atechofficials/protokeeb/Images/KB_Images/Protokeeb_1.png

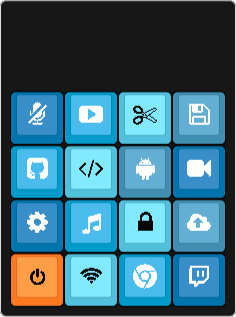
Images/KB_Images/Protokeeb_1.png
