atechofficials/protokeeb/Images/KB_Images/Protokeeb_3.jpg

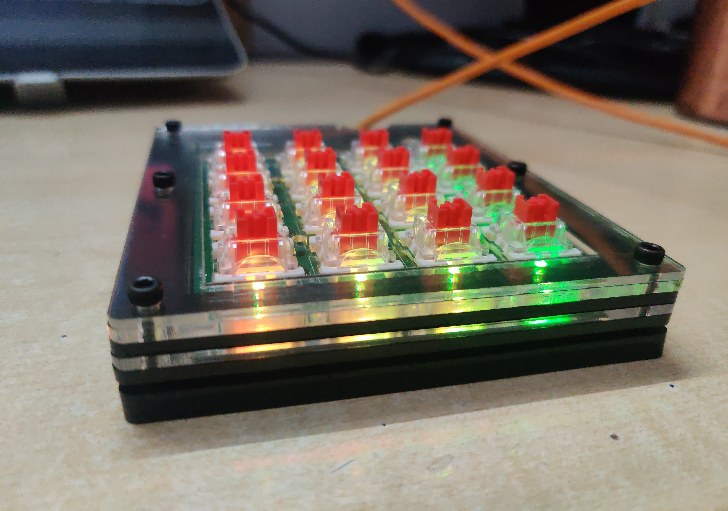
Images/KB_Images/Protokeeb_3.jpg
