atechofficials/protokeeb/Images/KB_Images/Protokeeb_3D-1.jpg

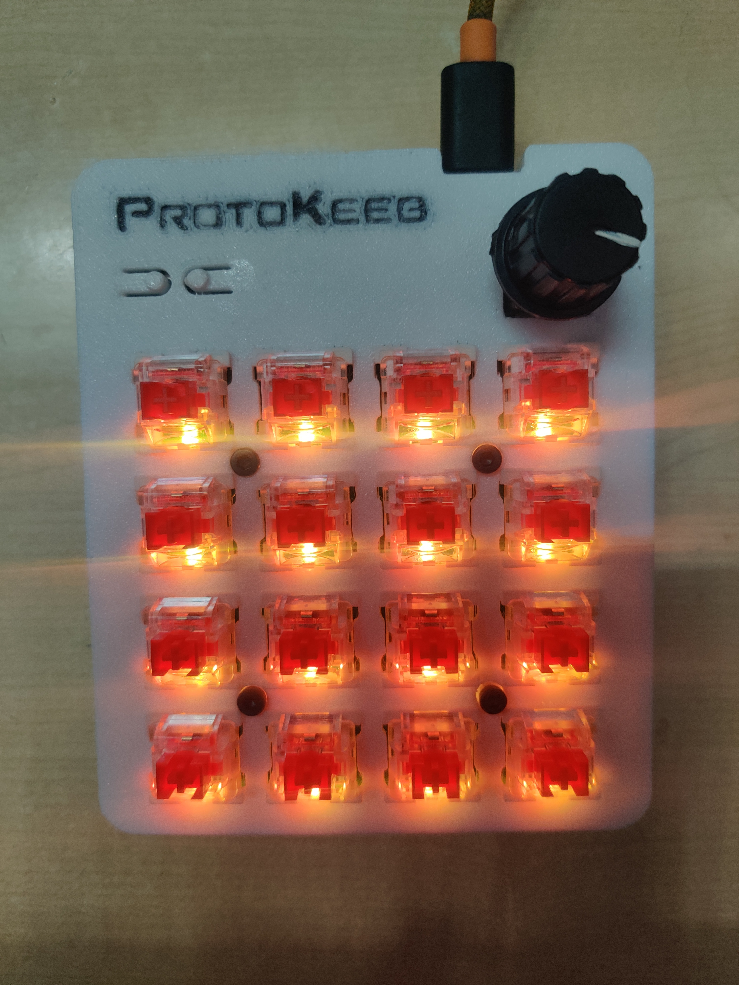
Images/KB_Images/Protokeeb_3D-1.jpg
