atechofficials/protokeeb/Images/KB_Images/Protokeeb_3D-2.jpg

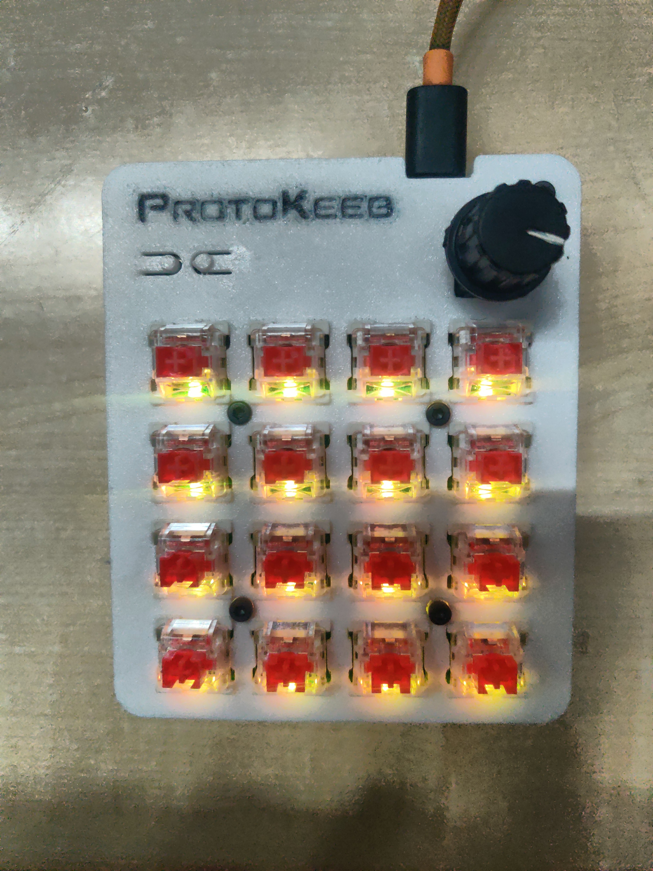
Images/KB_Images/Protokeeb_3D-2.jpg
