atechofficials/protokeeb/Images/KB_Images/Protokeeb_3D-3.jpg

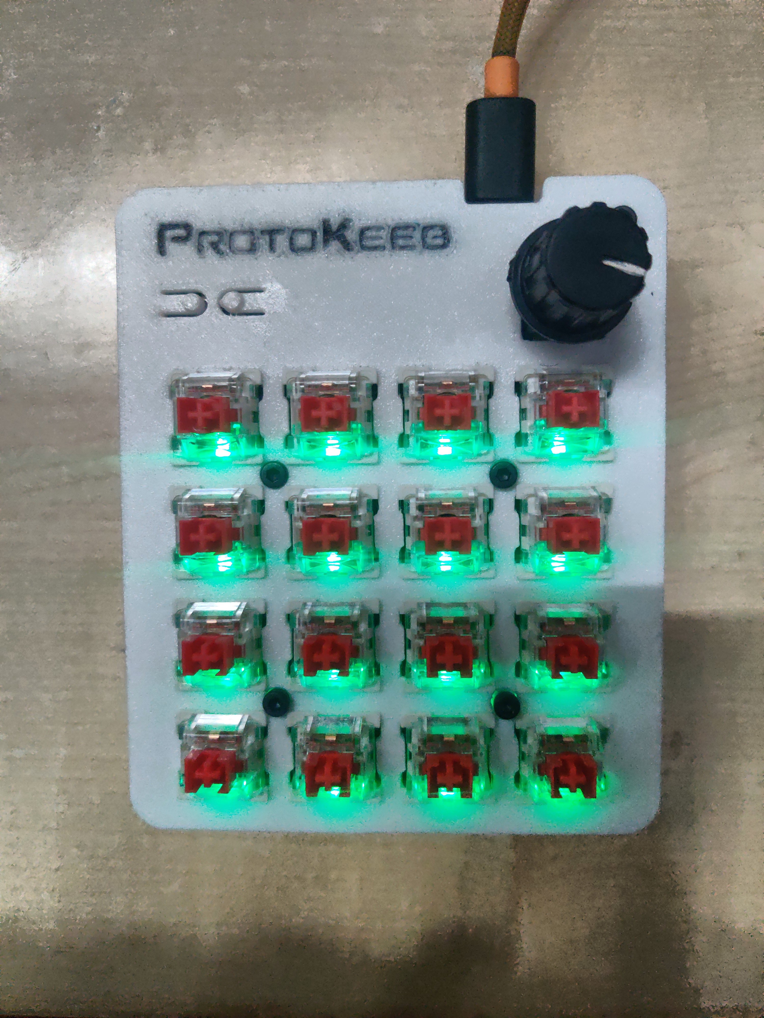
Images/KB_Images/Protokeeb_3D-3.jpg
