atechofficials/protokeeb/Images/KB_Images/Protokeeb_3D-4.jpg

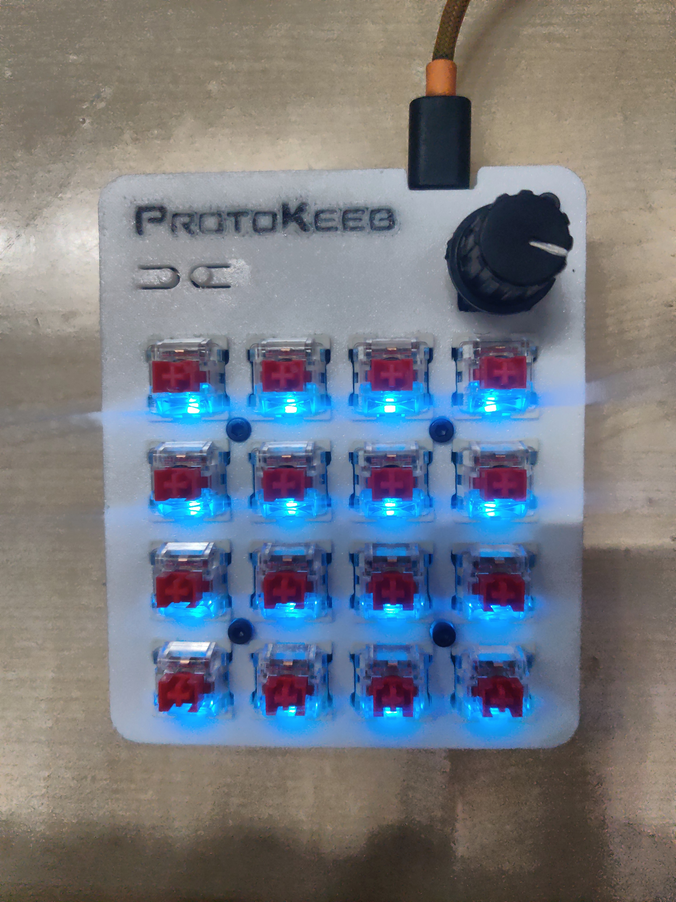
Images/KB_Images/Protokeeb_3D-4.jpg
