atechofficials/protokeeb/Images/KB_Images/Protokeeb_3D-5.jpg

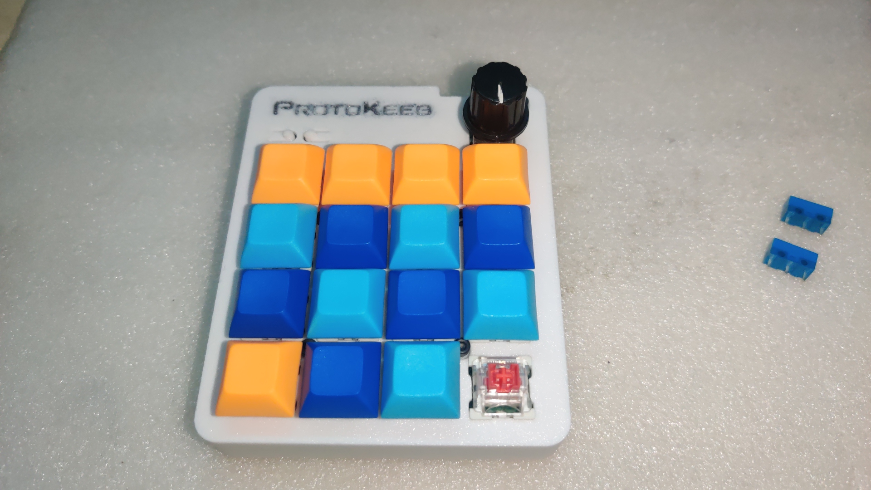
Images/KB_Images/Protokeeb_3D-5.jpg
