atechofficials/protokeeb/Images/KB_Images/Protokeeb_3D-6.jpg

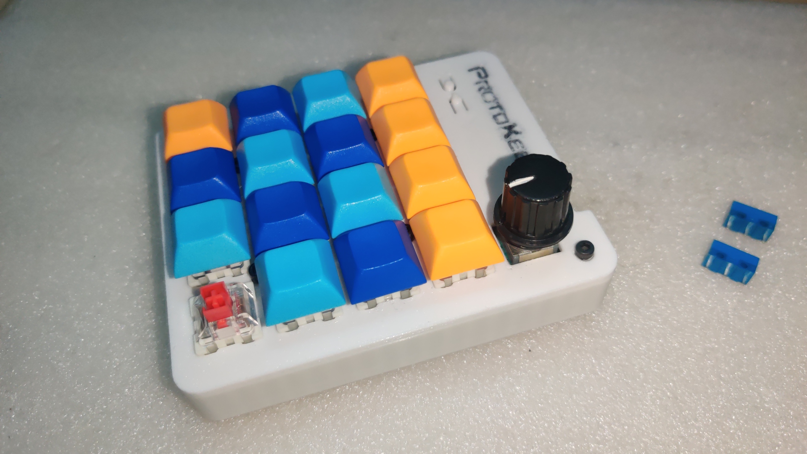
Images/KB_Images/Protokeeb_3D-6.jpg
