atechofficials/protokeeb/Images/KB_Images/Protokeeb_3D-7.jpg

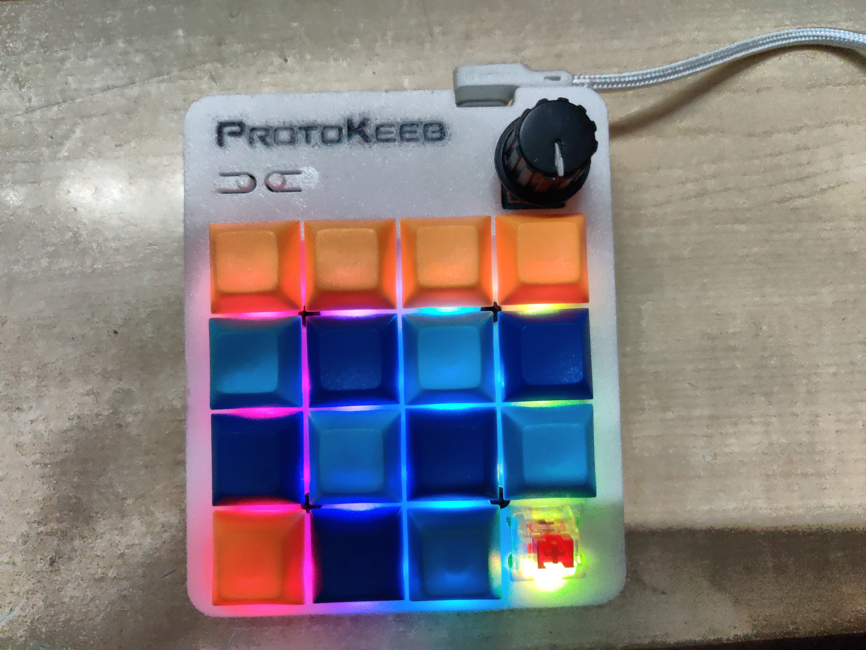
Images/KB_Images/Protokeeb_3D-7.jpg
