atechofficials/protokeeb/Images/KB_Images/Protokeeb_3D-8.jpg

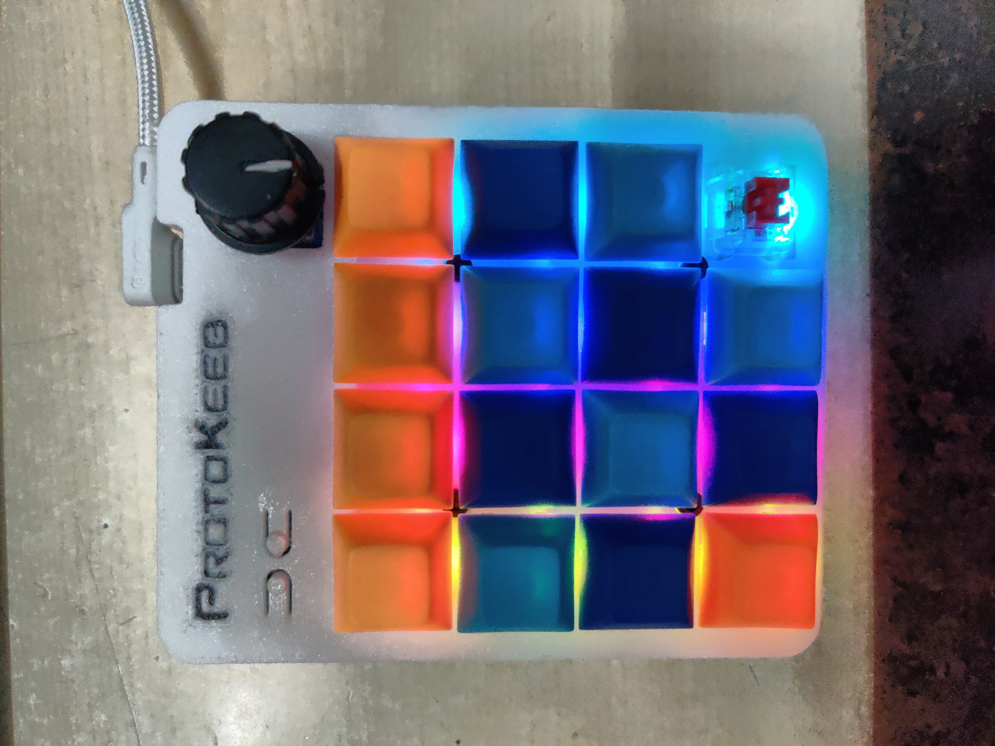
Images/KB_Images/Protokeeb_3D-8.jpg
