atechofficials/protokeeb/Images/KB_Images/Protokeeb_3D-9.jpg

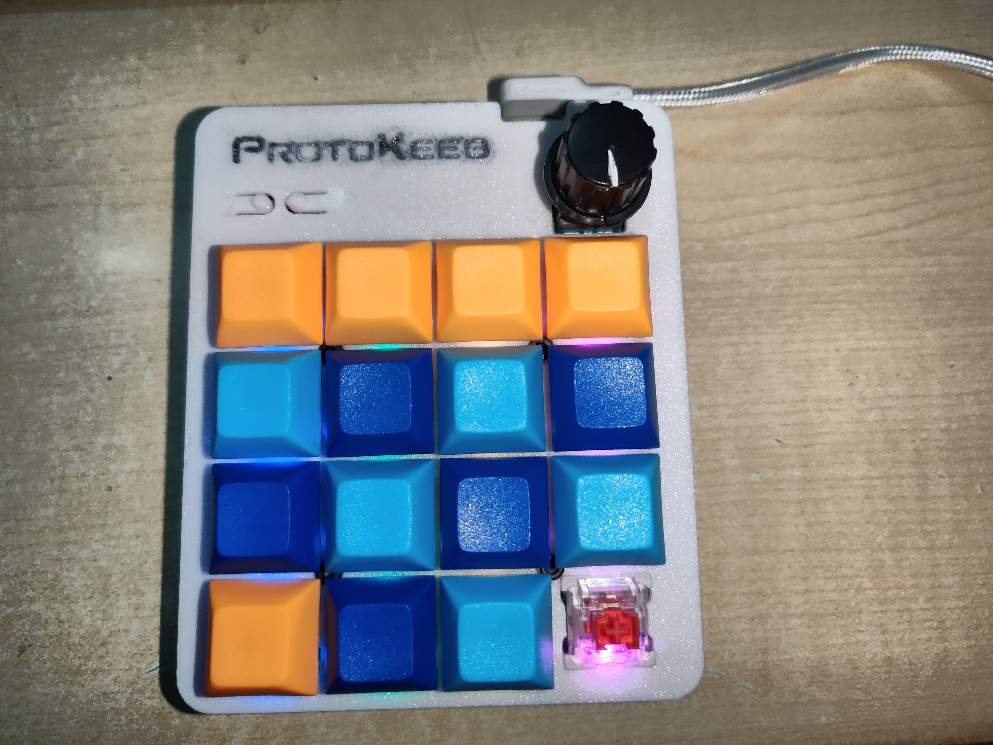
Images/KB_Images/Protokeeb_3D-9.jpg
