atechofficials/protokeeb/Images/KB_Images/Protokeeb_3D-10.jpg

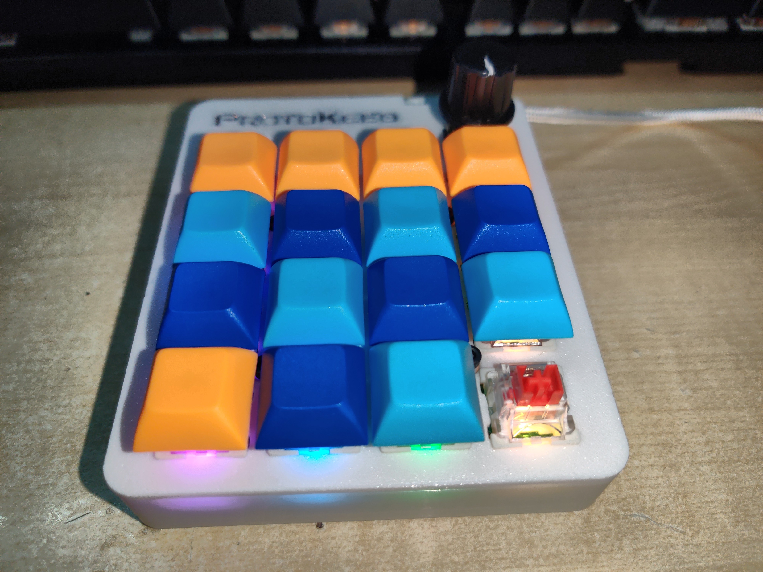
Images/KB_Images/Protokeeb_3D-10.jpg
