atechofficials/protokeeb/Images/KB_Images/Protokeeb_3D-11.jpg

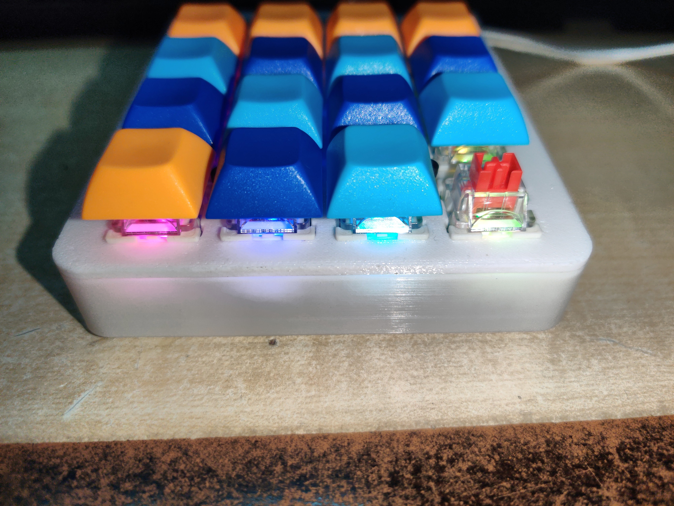
Images/KB_Images/Protokeeb_3D-11.jpg
