atechofficials/protokeeb/Images/KB_Images/Protokeeb_3D-14.jpg

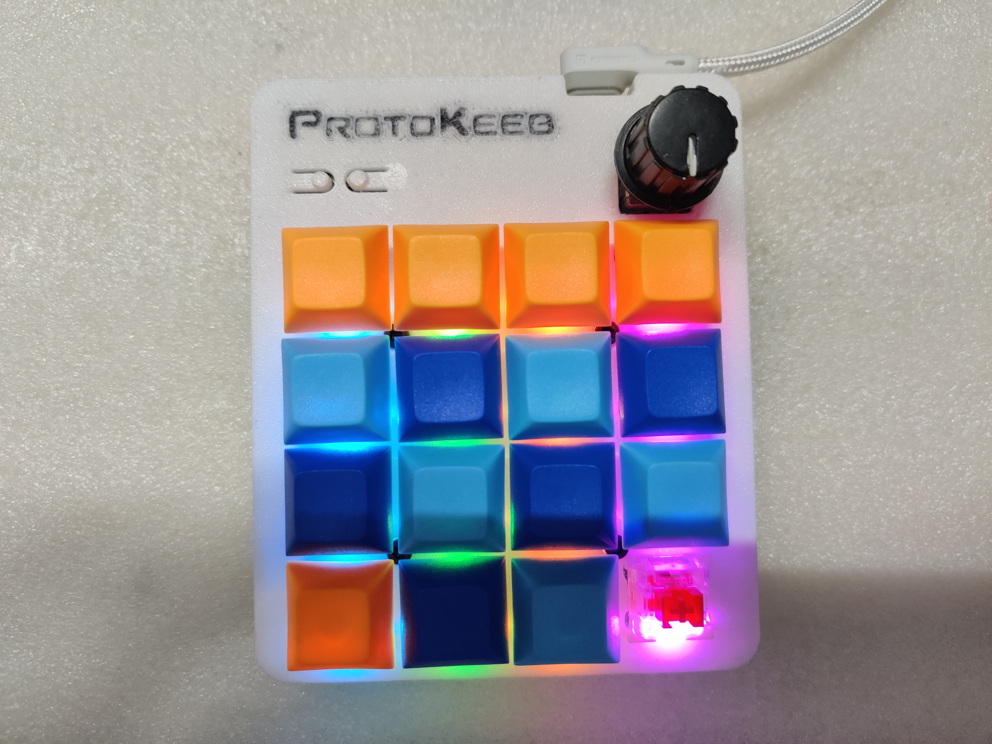
Images/KB_Images/Protokeeb_3D-14.jpg
