atechofficials/protokeeb/Images/KB_Images/Protokeeb_3D-15.jpg

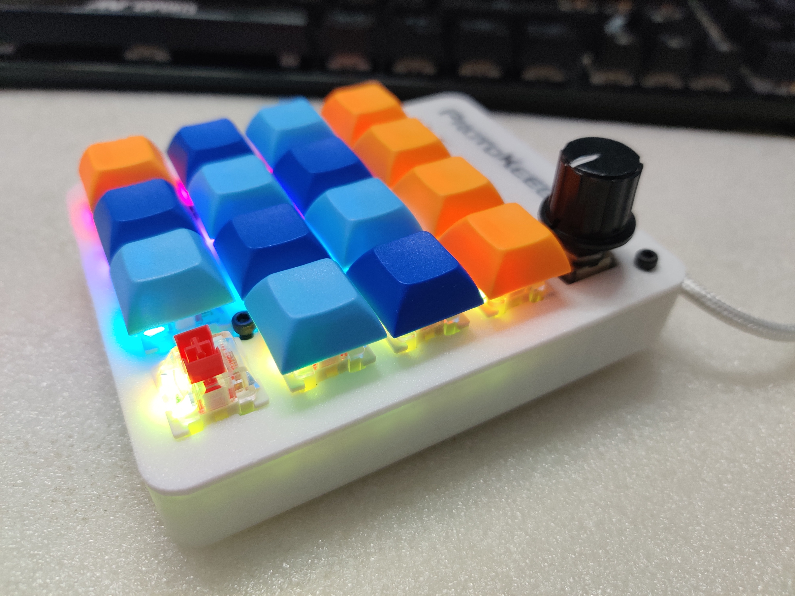
Images/KB_Images/Protokeeb_3D-15.jpg
