atechofficials/protokeeb/Images/KB_Images/Protokeeb_3D-16.jpg

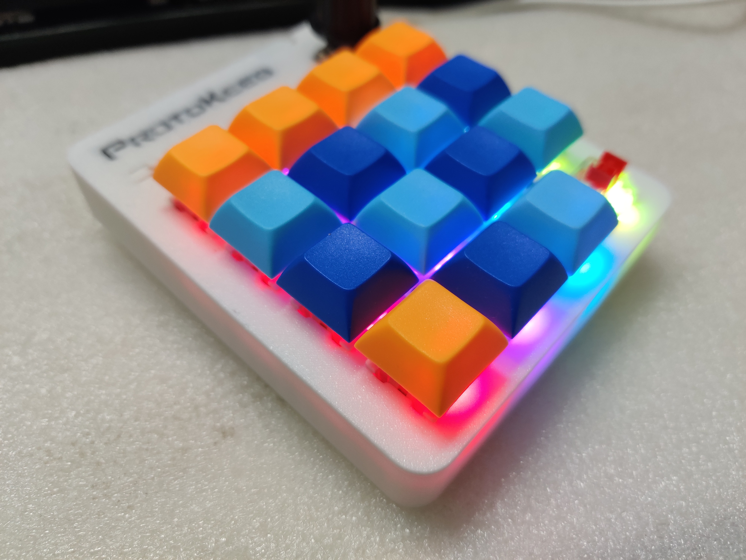
Images/KB_Images/Protokeeb_3D-16.jpg
