atechofficials/protokeeb/Images/KB_Images/Protokeeb_3D-17.jpg

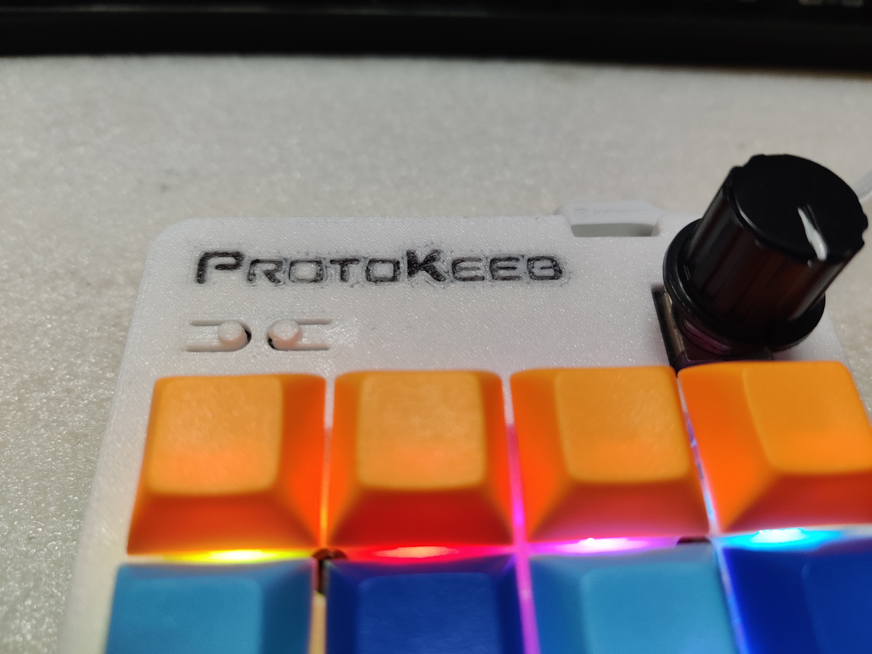
Images/KB_Images/Protokeeb_3D-17.jpg
