atechofficials/protokeeb/Images/KB_Images/Protokeeb_3D-18.jpg

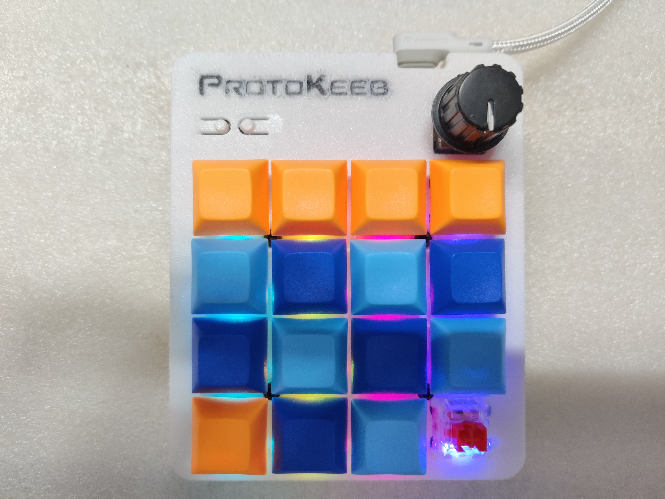
Images/KB_Images/Protokeeb_3D-18.jpg
