atechofficials/protokeeb/Images/KB_Images/Protokeeb_3D-19.jpg

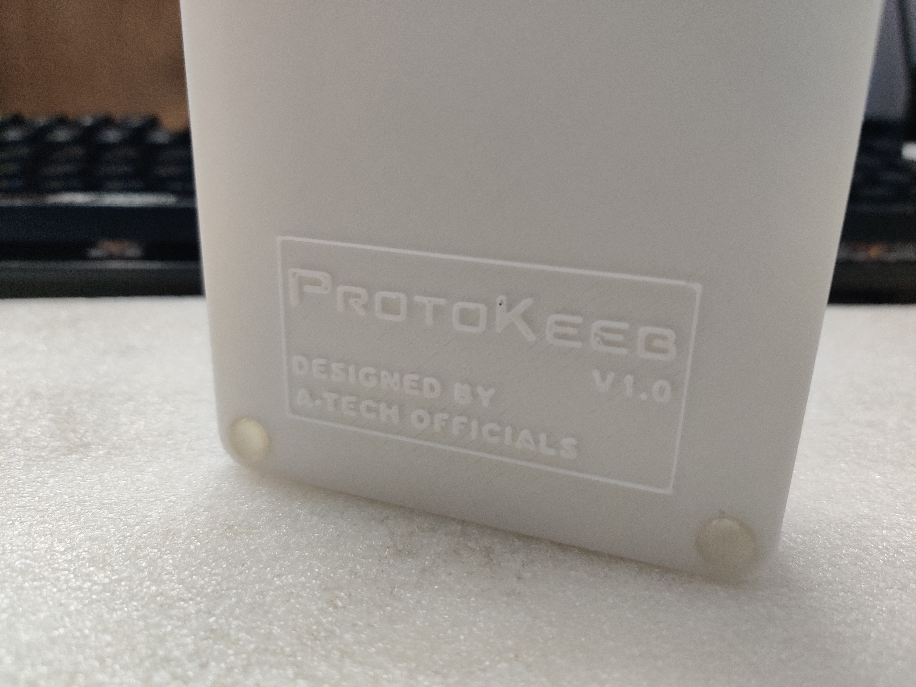
Images/KB_Images/Protokeeb_3D-19.jpg
