atechofficials/protokeeb/Images/KB_Images/Protokeeb_4.jpg

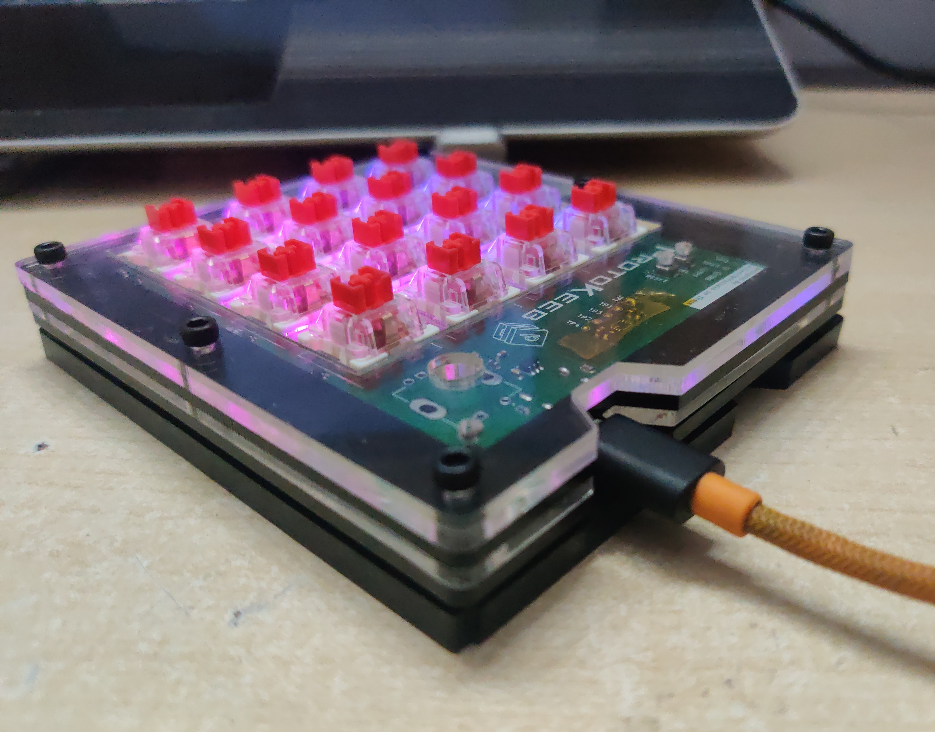
Images/KB_Images/Protokeeb_4.jpg
