atechofficials/protokeeb/Images/KB_Images/protokeeb_via_layout.png

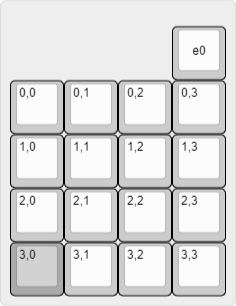
Images/KB_Images/protokeeb_via_layout.png
