atechofficials/protokeeb/Images/PCB_Images/Protokeeb_PCB_1.jpg

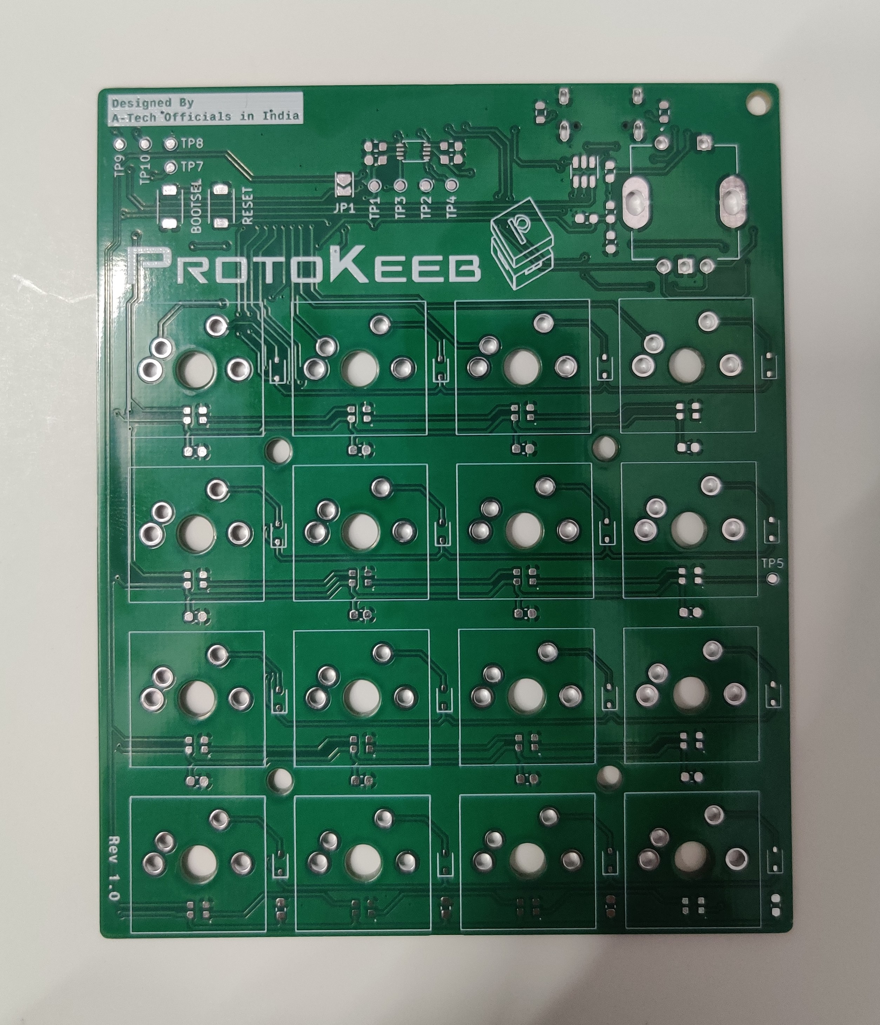
Images/PCB_Images/Protokeeb_PCB_1.jpg
