atechofficials/protokeeb/Images/PCB_Images/Protokeeb_PCB_2.jpg

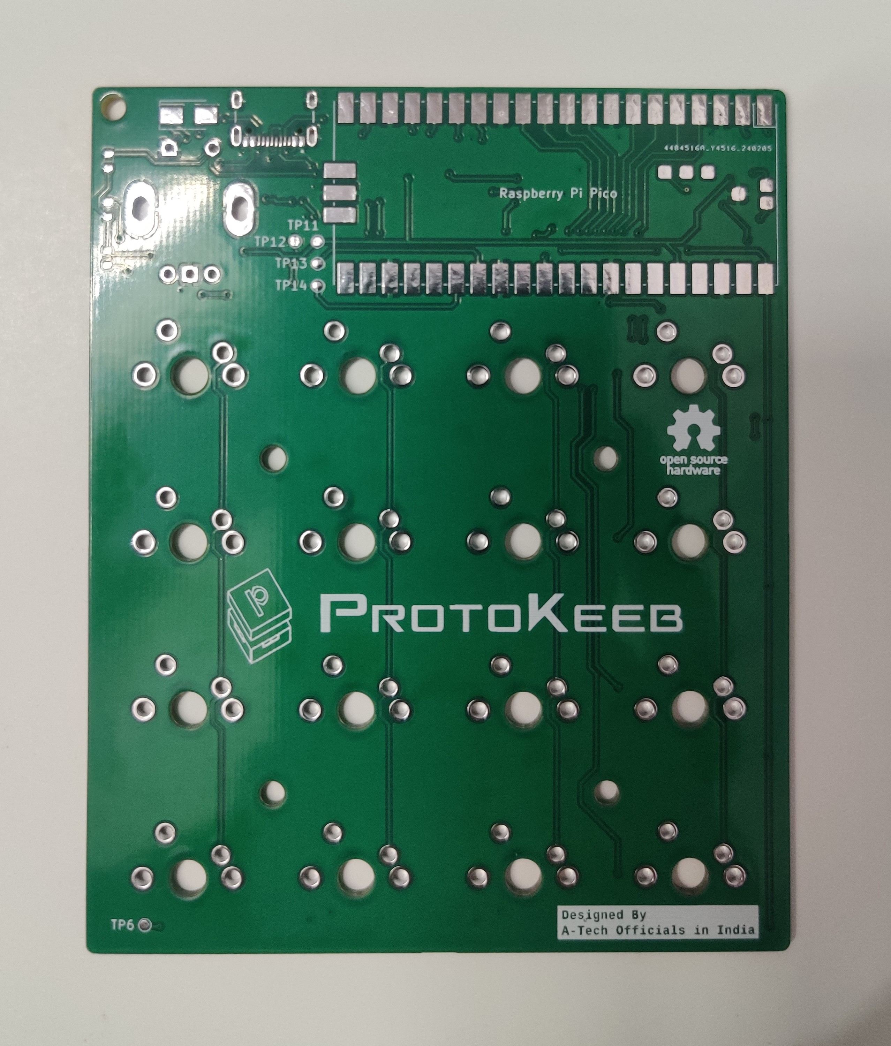
Images/PCB_Images/Protokeeb_PCB_2.jpg
