atechofficials/protokeeb/Images/PCB_Images/Protokeeb_PCB_3.jpg

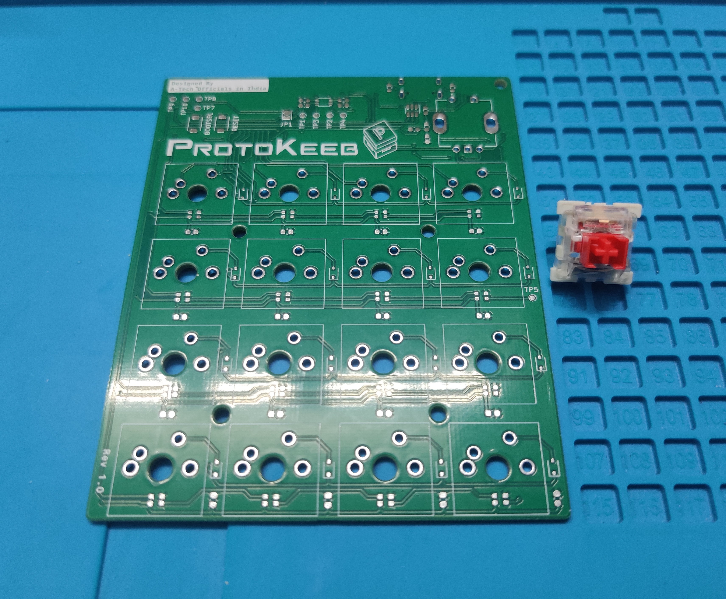
Images/PCB_Images/Protokeeb_PCB_3.jpg
