atechofficials/protokeeb/Images/PCB_Renders/AT-ProtoKeeb_rev1_1.png

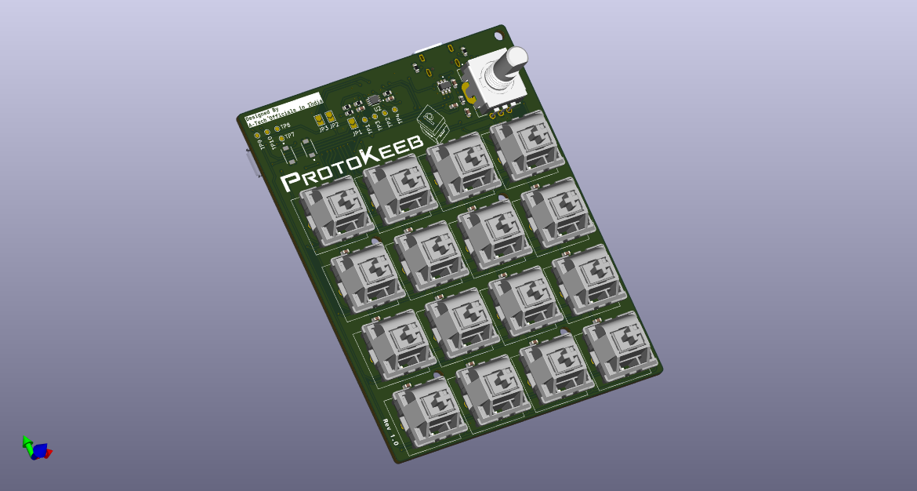
Images/PCB_Renders/AT-ProtoKeeb_rev1_1.png
