atechofficials/protokeeb/Images/PCB_Renders/AT-ProtoKeeb_rev1_2.png

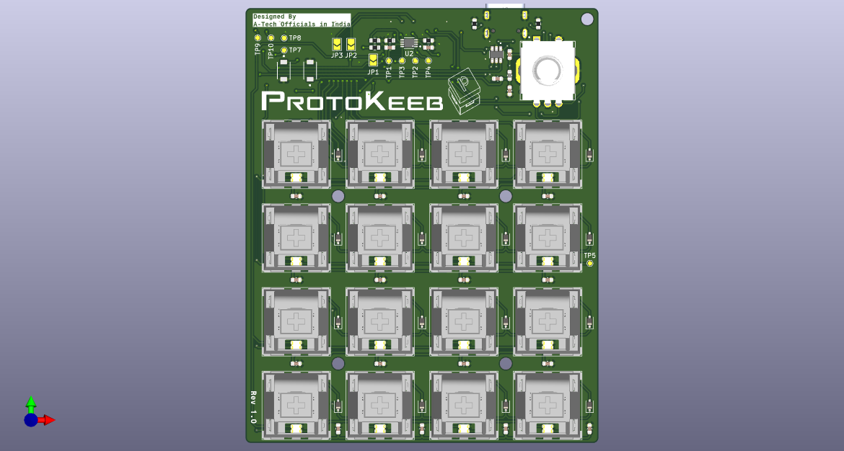
Images/PCB_Renders/AT-ProtoKeeb_rev1_2.png
