atechofficials/protokeeb/Images/PCB_Renders/AT-ProtoKeeb_rev1_3.png

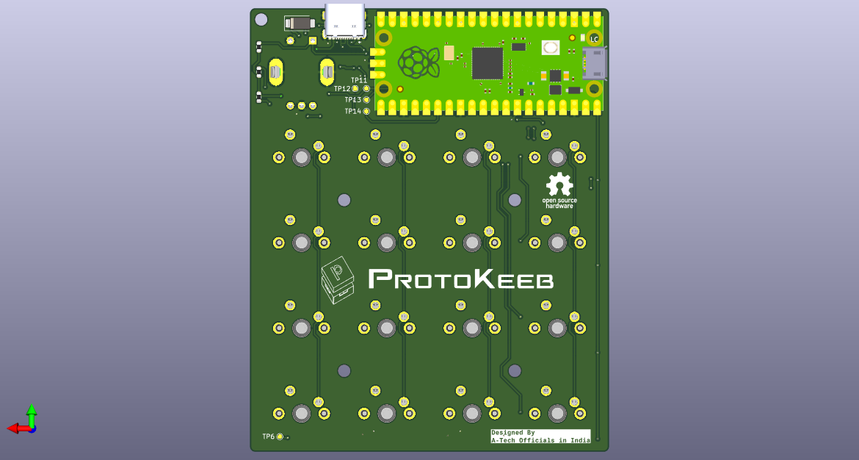
Images/PCB_Renders/AT-ProtoKeeb_rev1_3.png
