atechofficials/protokeeb/Images/PCB_Renders/AT-ProtoKeeb_rev1_4.png

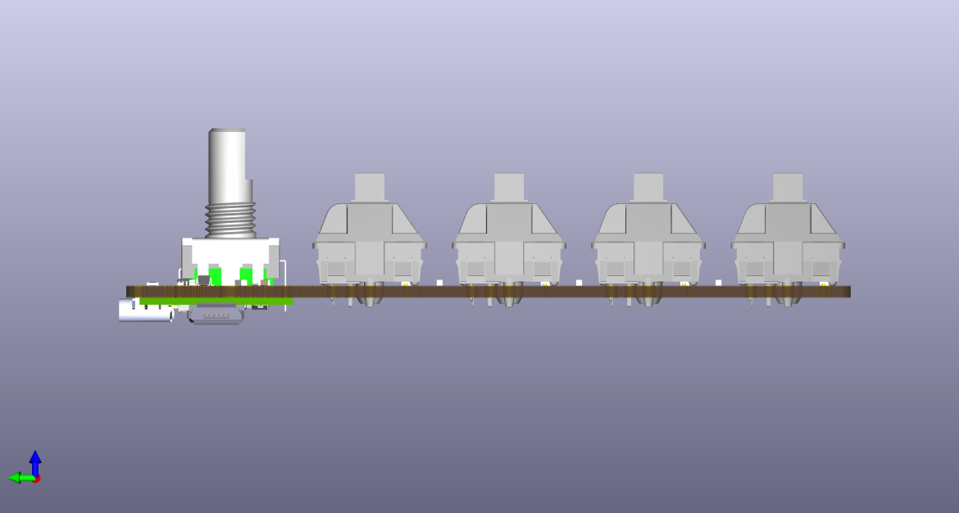
Images/PCB_Renders/AT-ProtoKeeb_rev1_4.png
