atechofficials/protokeeb/Images/PCB_Renders/AT-ProtoKeeb_rev1_6.png

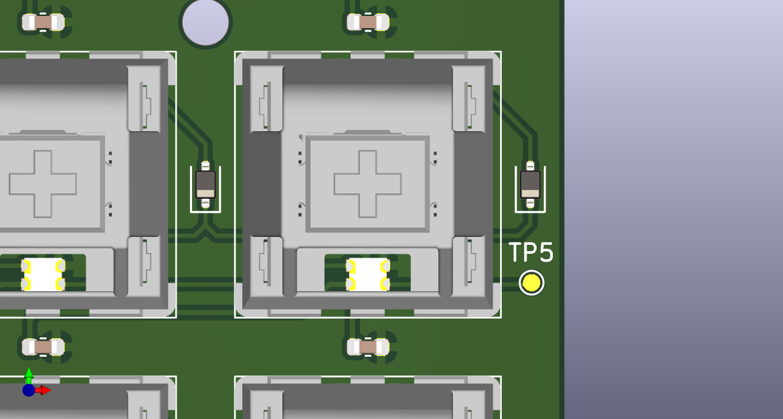
Images/PCB_Renders/AT-ProtoKeeb_rev1_6.png
