atechofficials/protokeeb/Images/PCB_Renders/AT-ProtoKeeb_rev1_7.png

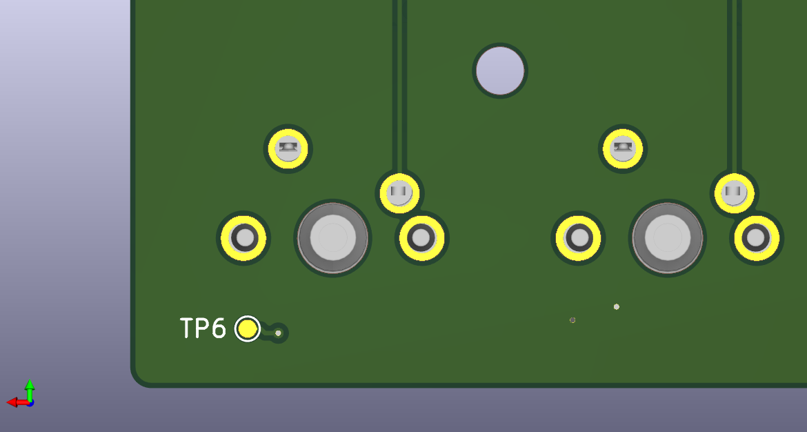
Images/PCB_Renders/AT-ProtoKeeb_rev1_7.png
