atechofficials/protokeeb/Images/PCB_Renders/AT-ProtoKeeb_rev1_8.png

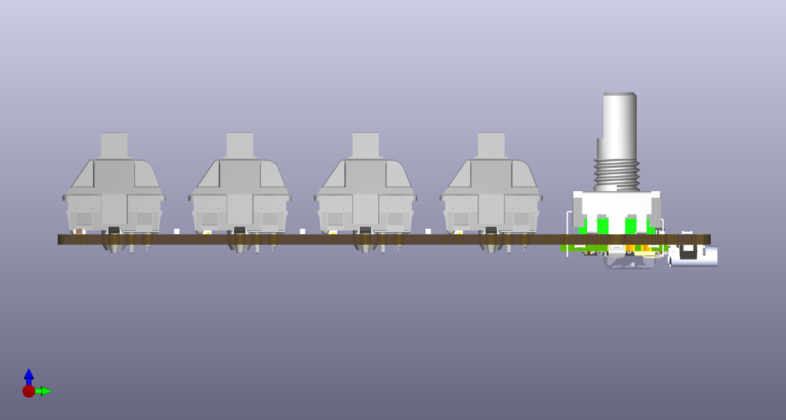
Images/PCB_Renders/AT-ProtoKeeb_rev1_8.png
