atechofficials/protokeeb/Images/PCB_Renders/AT-ProtoKeeb_rev1_9.png

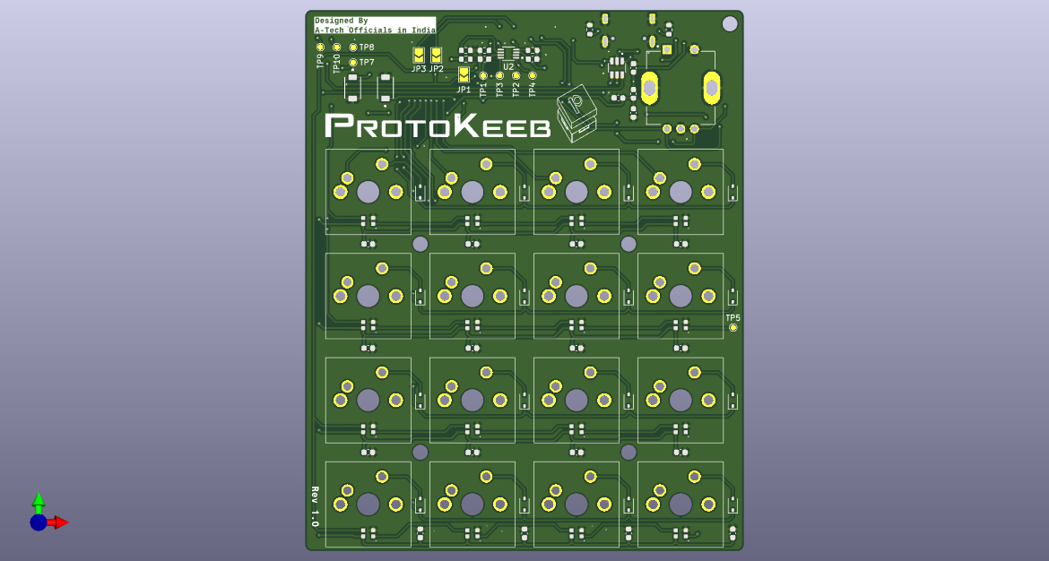
Images/PCB_Renders/AT-ProtoKeeb_rev1_9.png
