atechofficials/protokeeb/Images/Sandwich_Case/Protokeeb_SC_2.jpg

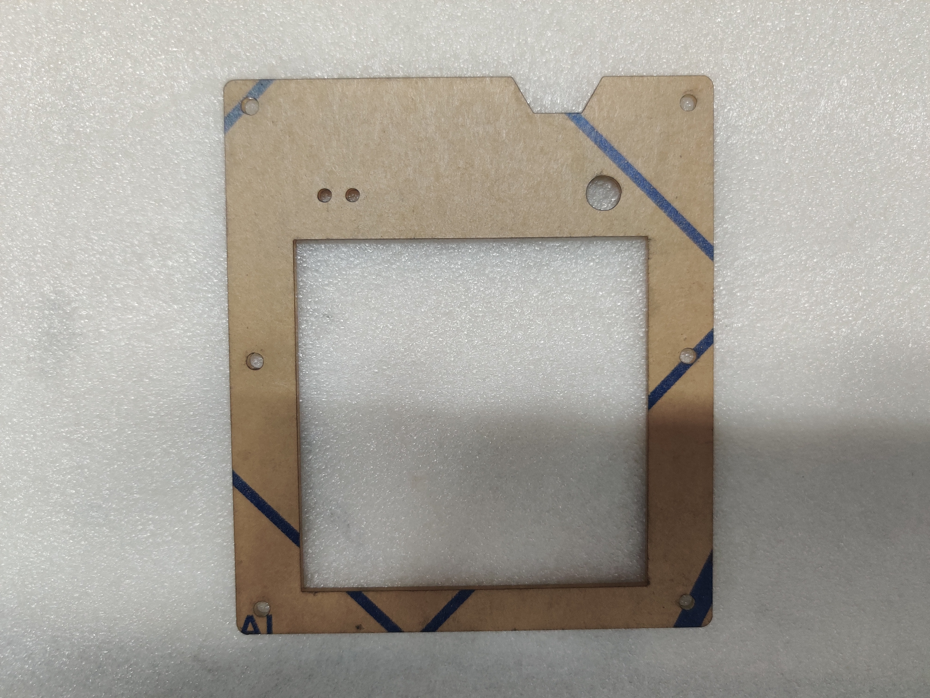
Images/Sandwich_Case/Protokeeb_SC_2.jpg
