atechofficials/protokeeb/Images/Sandwich_Case/Protokeeb_SC_3.jpg

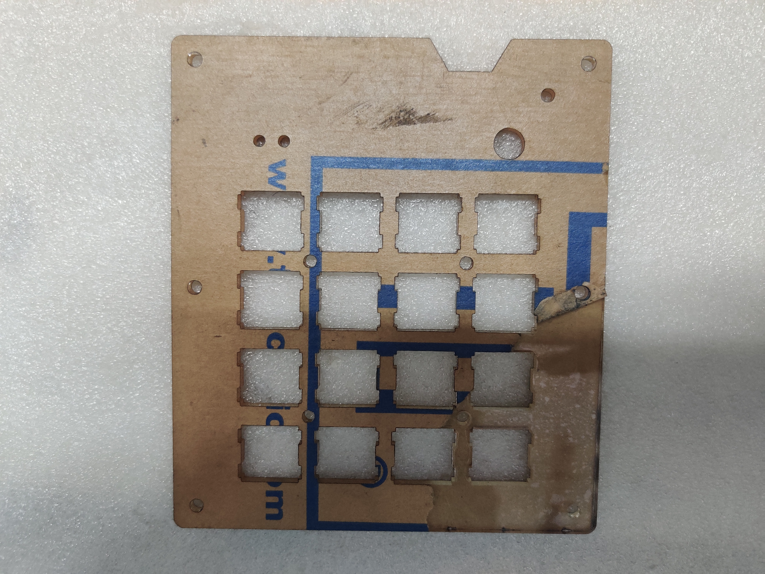
Images/Sandwich_Case/Protokeeb_SC_3.jpg
