atechofficials/protokeeb/Images/Sandwich_Case/Protokeeb_SC_7.jpg

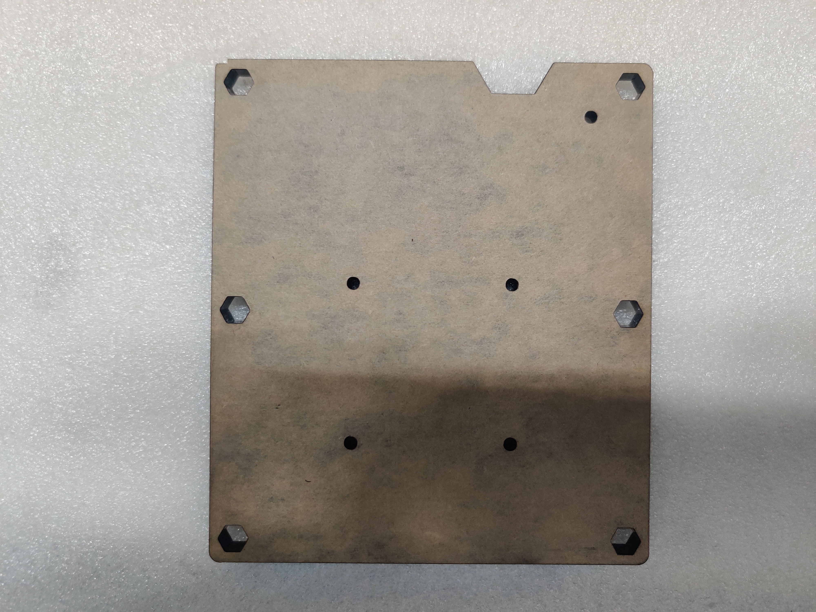
Images/Sandwich_Case/Protokeeb_SC_7.jpg
