atechofficials/protokeeb/Images/Sandwich_Case/Protokeeb_SC_8.jpg

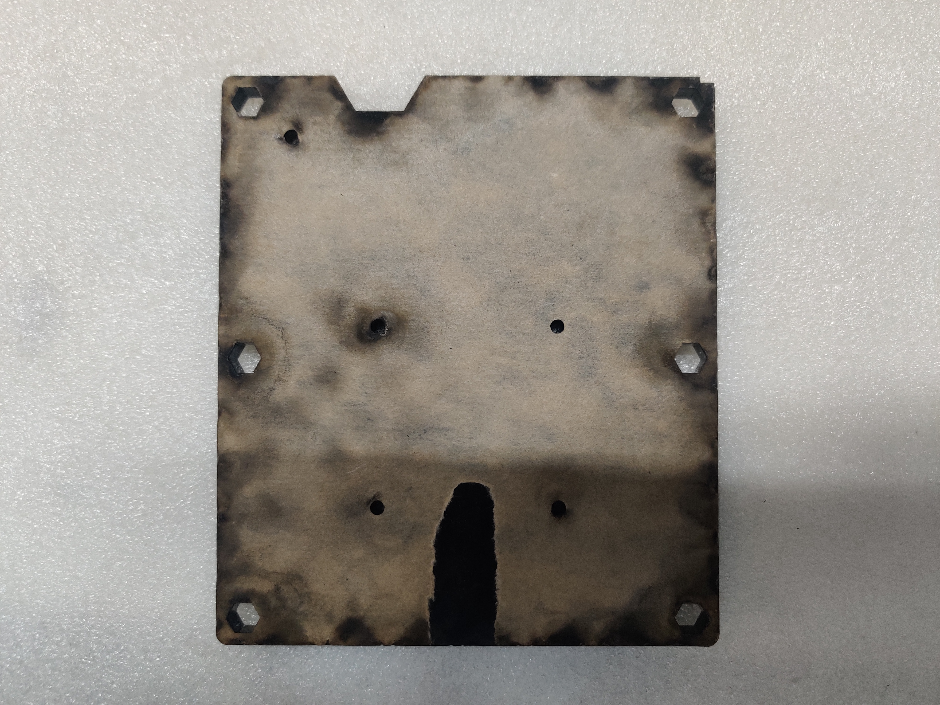
Images/Sandwich_Case/Protokeeb_SC_8.jpg
