atechofficials/protokeeb/PCB/Rev1.0/AT-ProtoKeeb_rev1/Datasheets/M2.5X5mm_Philips_Round_Head_Screw_Dim_1.webp

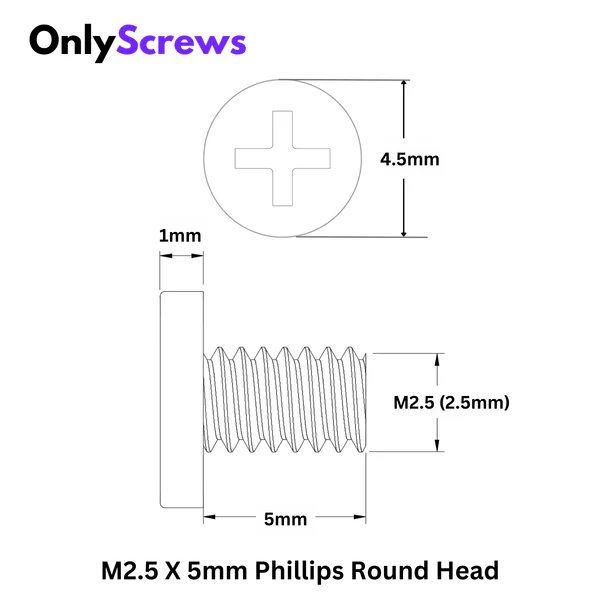
PCB/Rev1.0/AT-ProtoKeeb_rev1/Datasheets/M2.5X5mm_Philips_Round_Head_Screw_Dim_1.webp
