atechofficials/protokeeb/PCB/Rev1.0/AT-ProtoKeeb_rev1/Datasheets/M2.5x6mm_Brass_Insert_Dimensions_1.webp

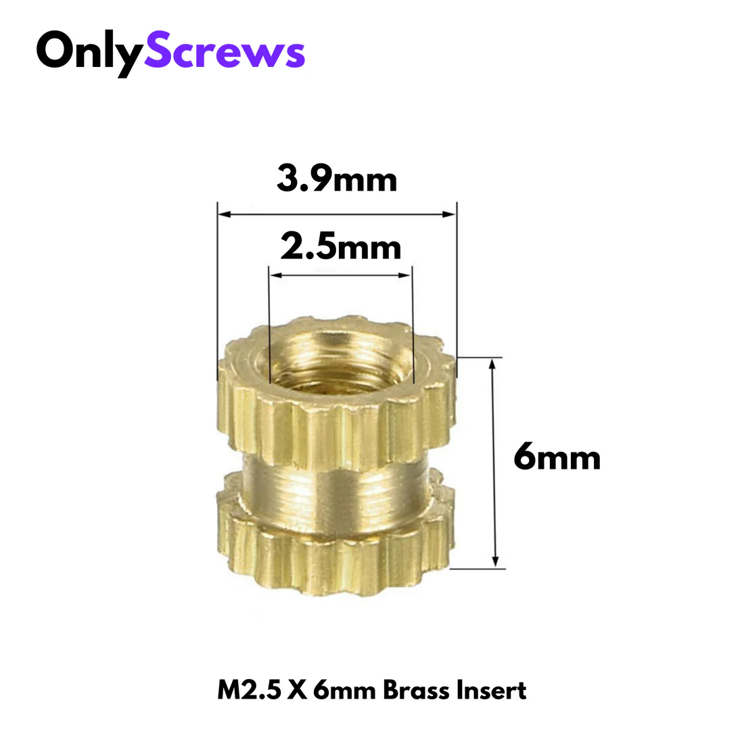
PCB/Rev1.0/AT-ProtoKeeb_rev1/Datasheets/M2.5x6mm_Brass_Insert_Dimensions_1.webp
