atechofficials/protokeeb/Images/3D_Printed_Case/3D_Case_4.jpg

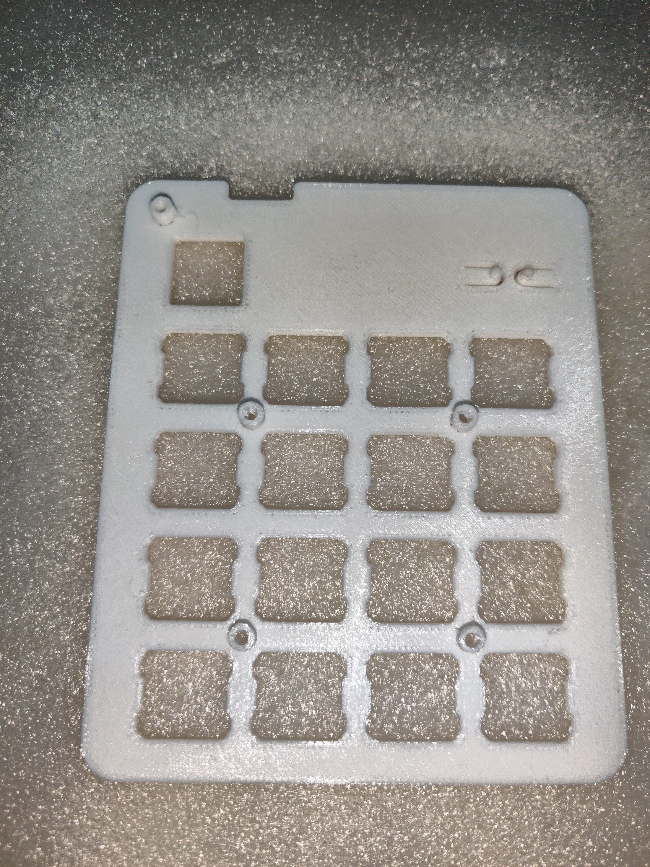
Images/3D_Printed_Case/3D_Case_4.jpg
