atechofficials/protokeeb/Images/3D_Printed_Case/3D_Case_6.jpg

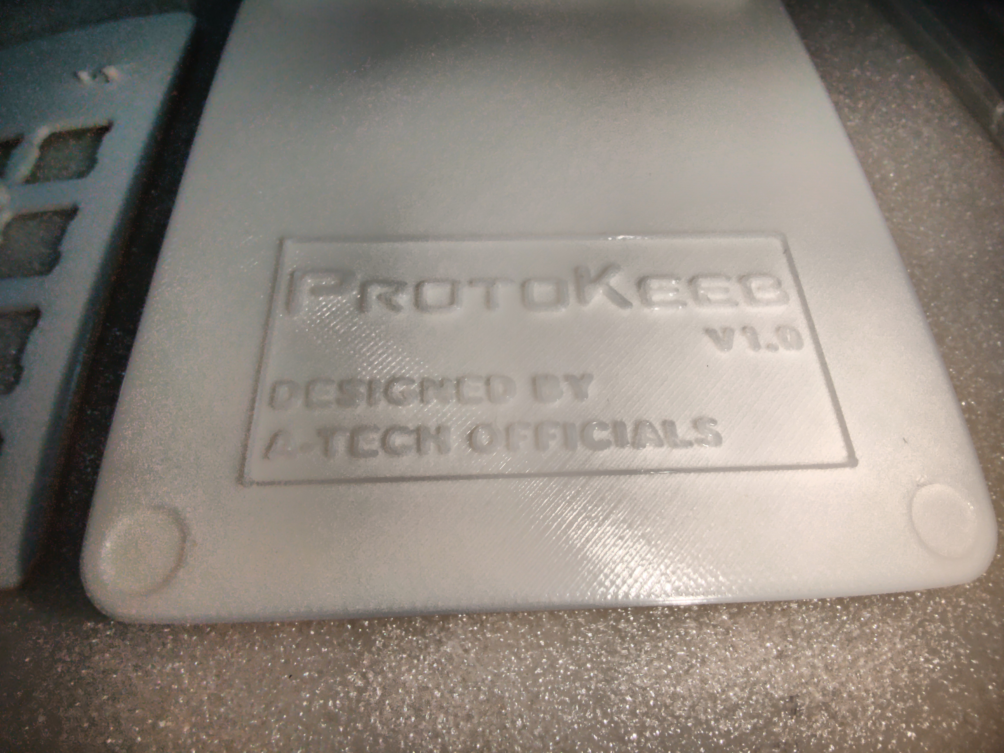
Images/3D_Printed_Case/3D_Case_6.jpg
