atechofficials/protokeeb/Images/3D_Printed_Case/3D_Case_12.jpg

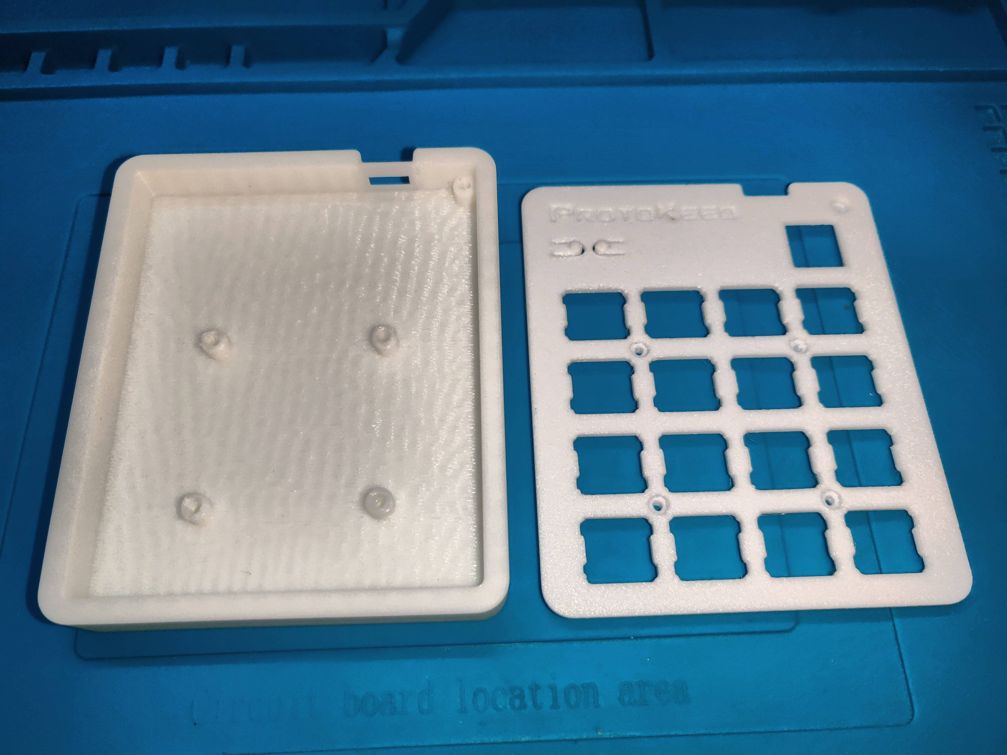
Images/3D_Printed_Case/3D_Case_12.jpg
