atechofficials/protokeeb/Images/3D_Printed_Case/3D_Case_13.jpg

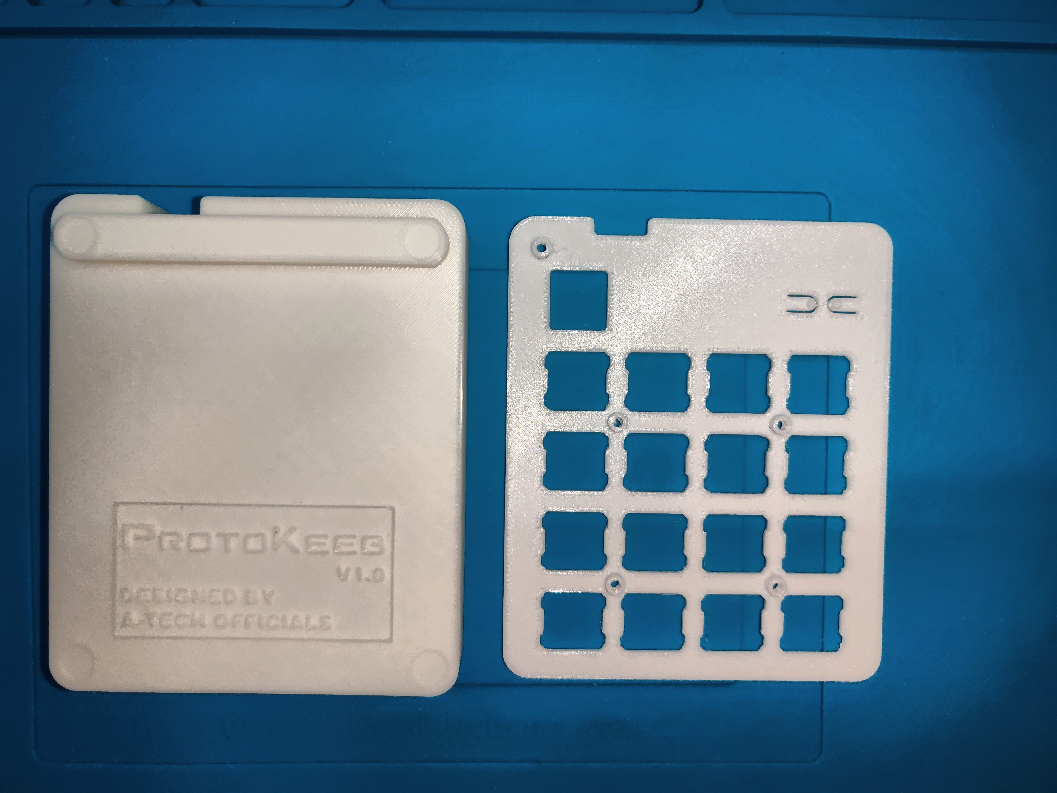
Images/3D_Printed_Case/3D_Case_13.jpg
