atechofficials/protokeeb/Images/3D_Printed_Case/Assembly/3D_Case_AS-64.jpg

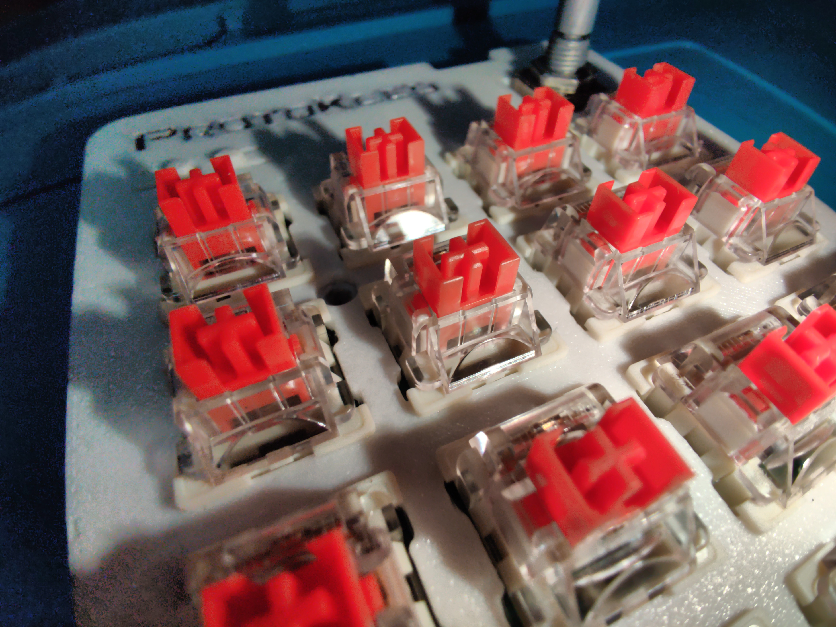
Images/3D_Printed_Case/Assembly/3D_Case_AS-64.jpg
