atechofficials/protokeeb/Images/3D_Printed_Case/Assembly/Threaded_Brass_Inserts_Soldering_Tip_4.jpg

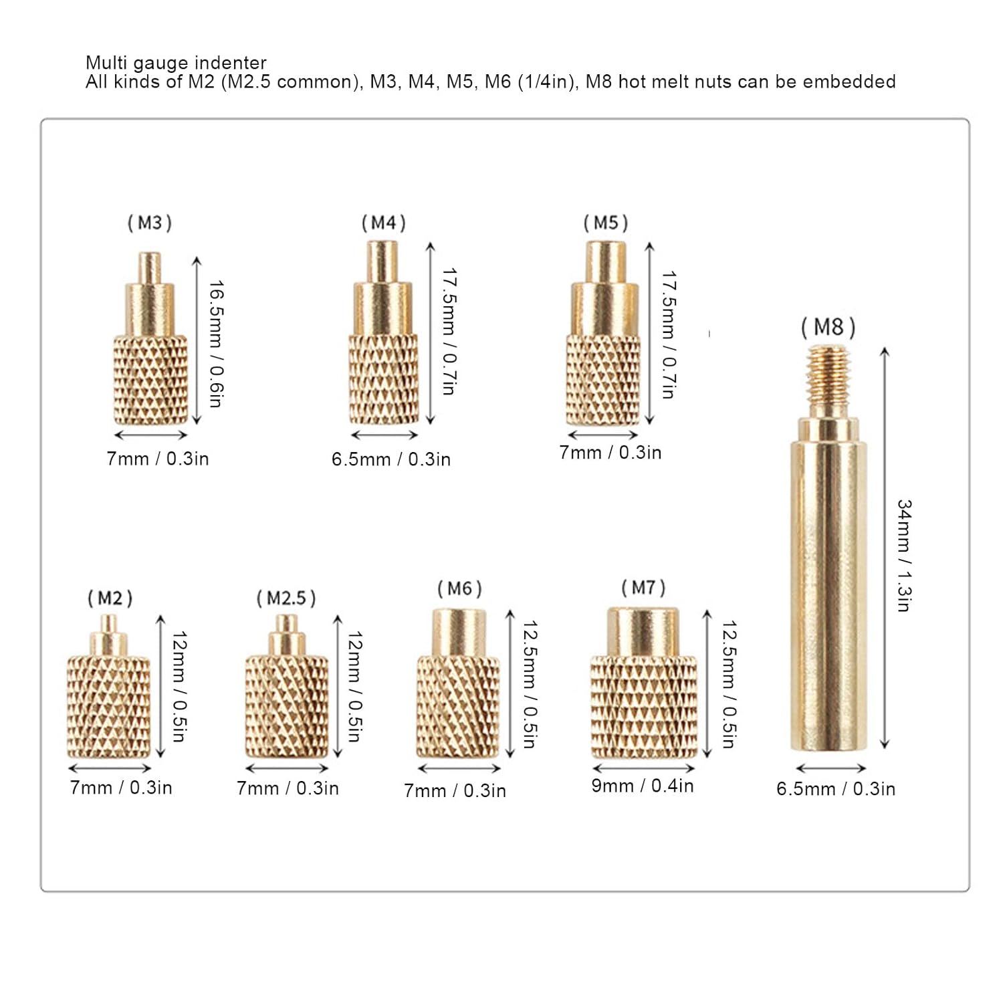
Images/3D_Printed_Case/Assembly/Threaded_Brass_Inserts_Soldering_Tip_4.jpg
