atechofficials/protokeeb/Images/PCB_Assembly/Protokeeb_AS_6.jpg

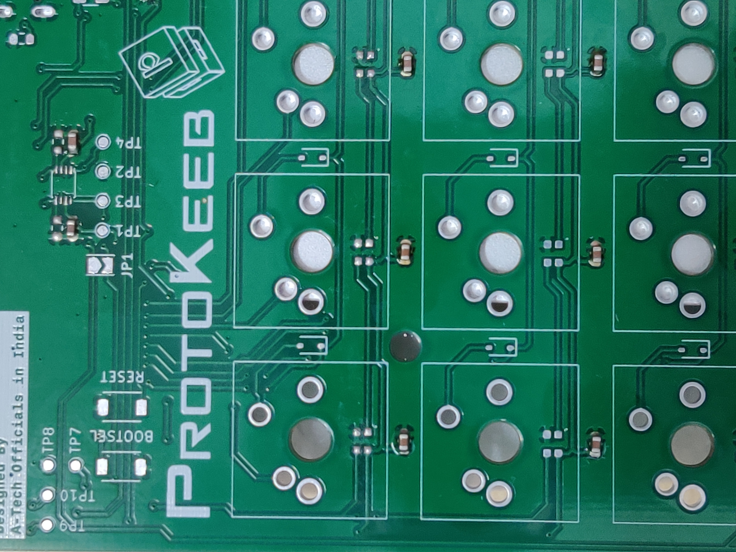
Images/PCB_Assembly/Protokeeb_AS_6.jpg
