atechofficials/protokeeb/Images/PCB_Assembly/Protokeeb_AS_7.jpg

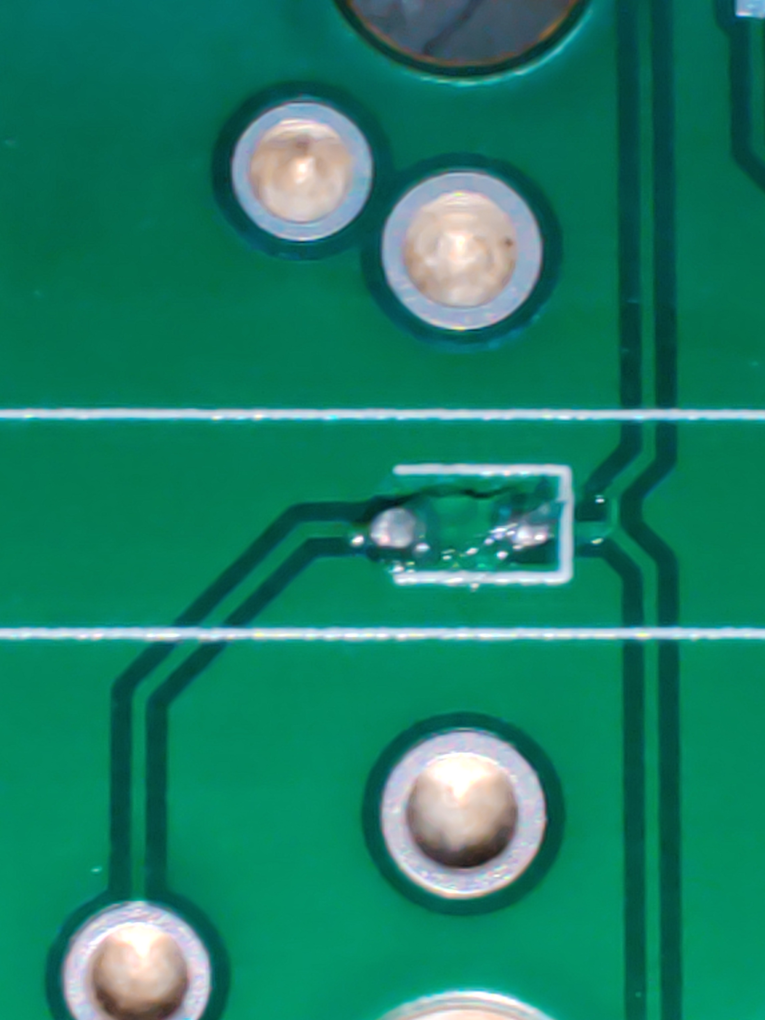
Images/PCB_Assembly/Protokeeb_AS_7.jpg
