atechofficials/protokeeb/Images/PCB_Assembly/Protokeeb_AS_9.jpg

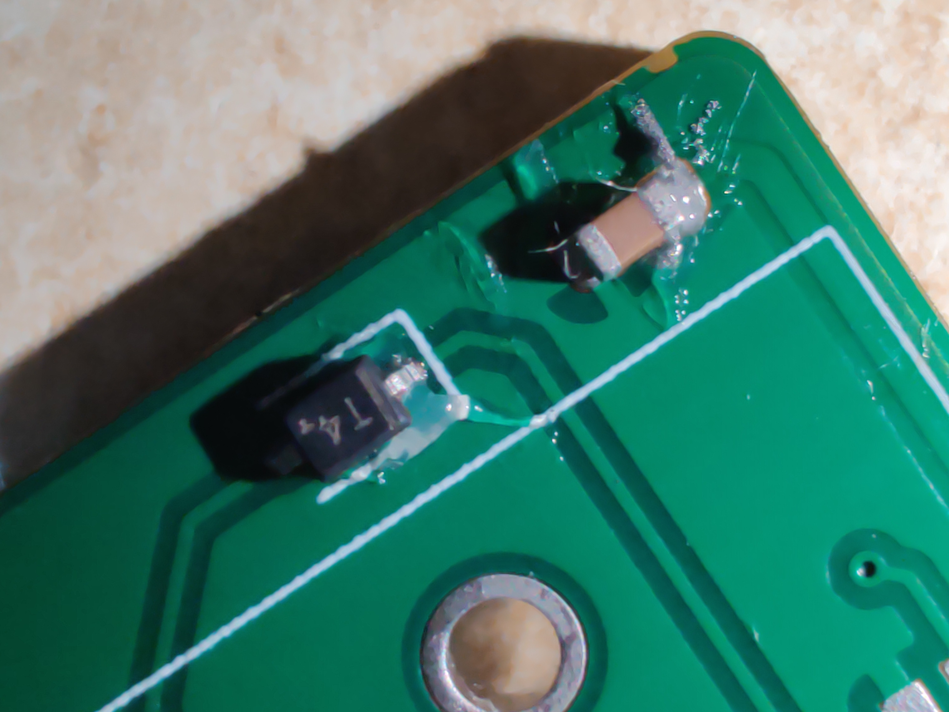
Images/PCB_Assembly/Protokeeb_AS_9.jpg
