atechofficials/protokeeb/Images/PCB_Assembly/Protokeeb_AS_10.jpg

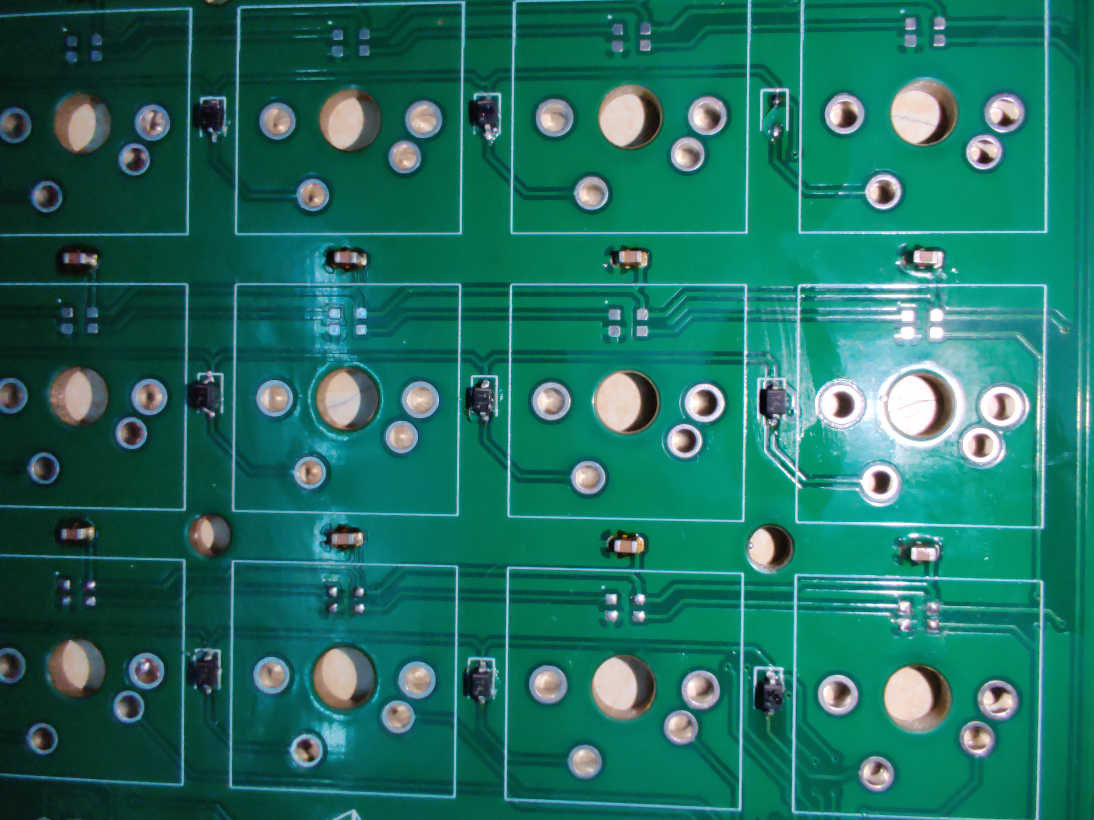
Images/PCB_Assembly/Protokeeb_AS_10.jpg
