atechofficials/protokeeb/Images/PCB_Assembly/Protokeeb_AS_14.jpg

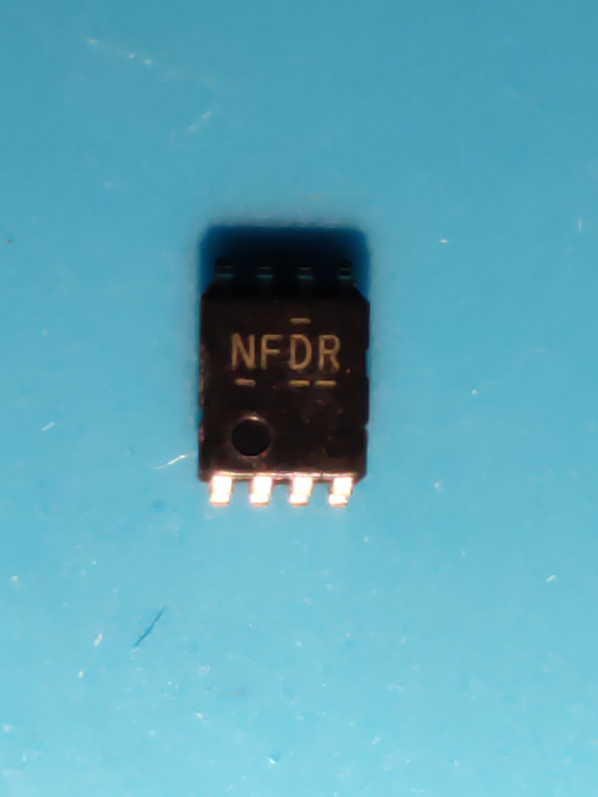
Images/PCB_Assembly/Protokeeb_AS_14.jpg
