atechofficials/protokeeb/Images/PCB_Assembly/Protokeeb_AS_17.jpg

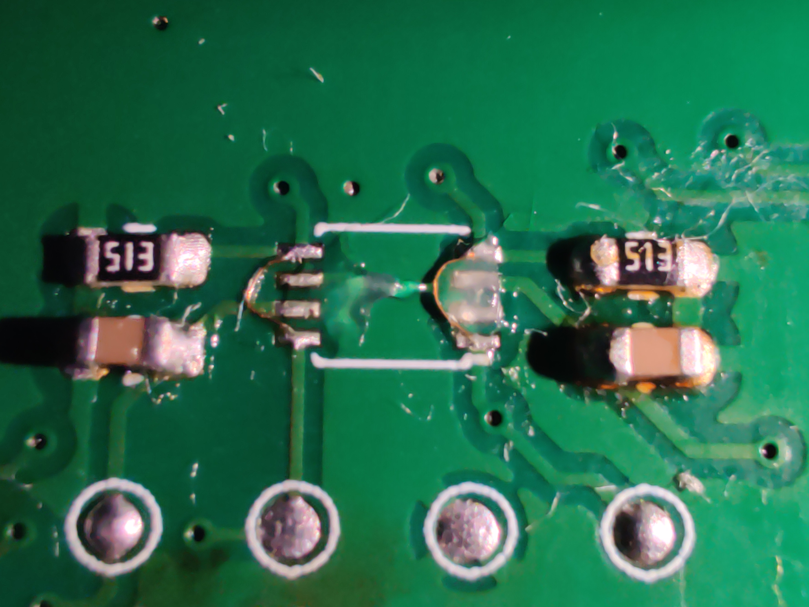
Images/PCB_Assembly/Protokeeb_AS_17.jpg
