atechofficials/protokeeb/Images/PCB_Assembly/Protokeeb_AS_21.jpg

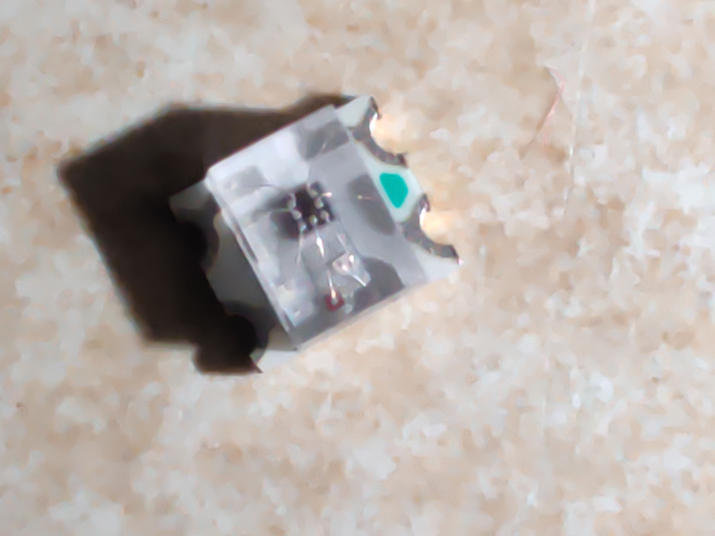
Images/PCB_Assembly/Protokeeb_AS_21.jpg
