atechofficials/protokeeb/Images/PCB_Assembly/Protokeeb_AS_22.jpg

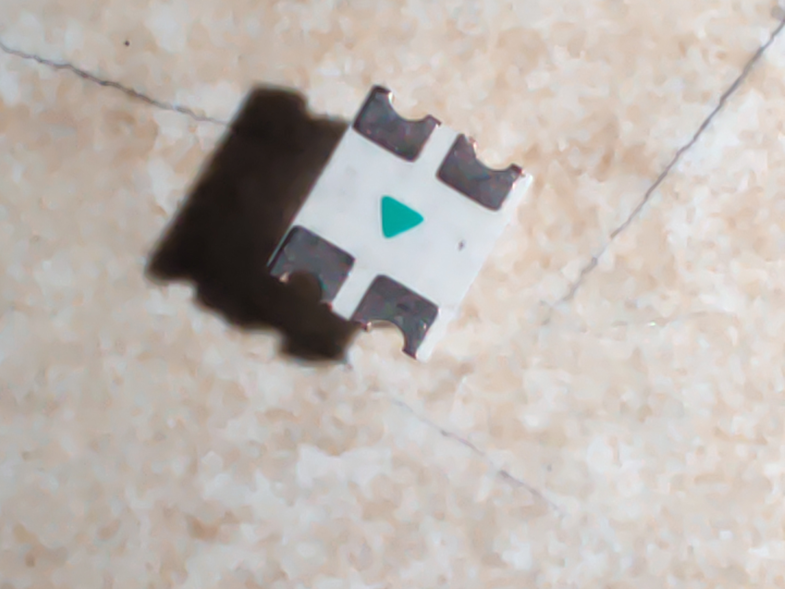
Images/PCB_Assembly/Protokeeb_AS_22.jpg
