atechofficials/protokeeb/Images/PCB_Assembly/Protokeeb_AS_25.jpg

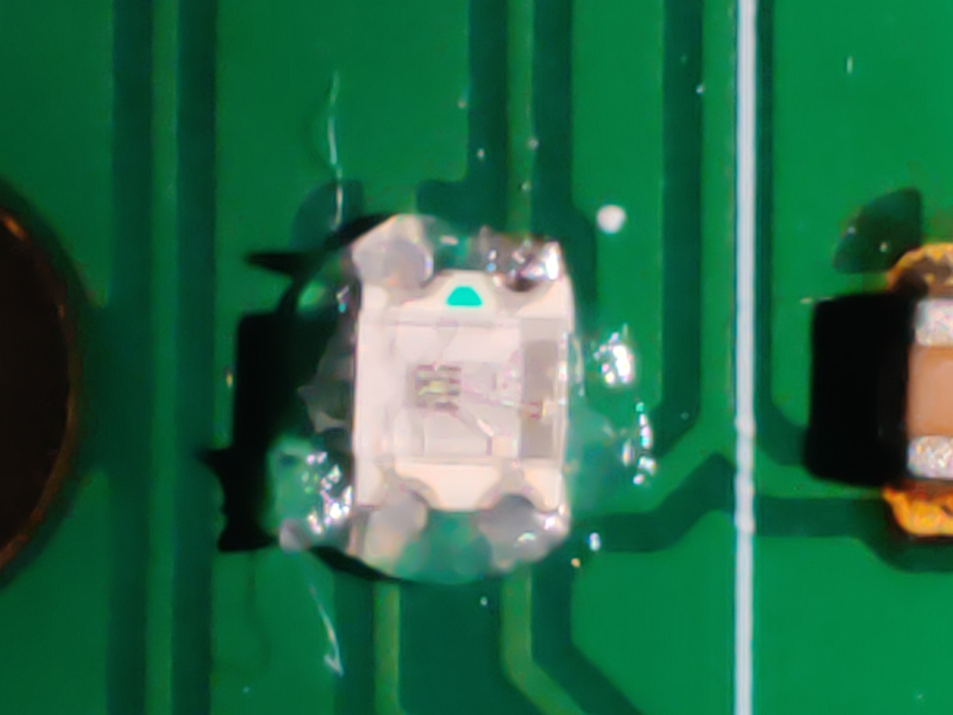
Images/PCB_Assembly/Protokeeb_AS_25.jpg
