atechofficials/protokeeb/Images/PCB_Assembly/Protokeeb_AS_47.jpg

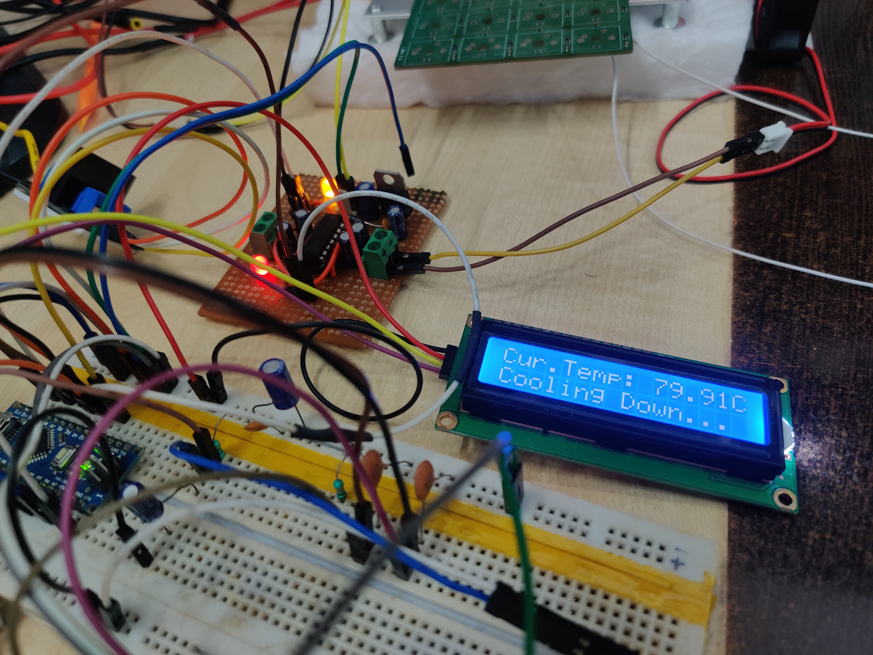
Images/PCB_Assembly/Protokeeb_AS_47.jpg
