atechofficials/protokeeb/Images/Sandwich_Case/Assembly/Sandwich_Case_AS_5.jpg

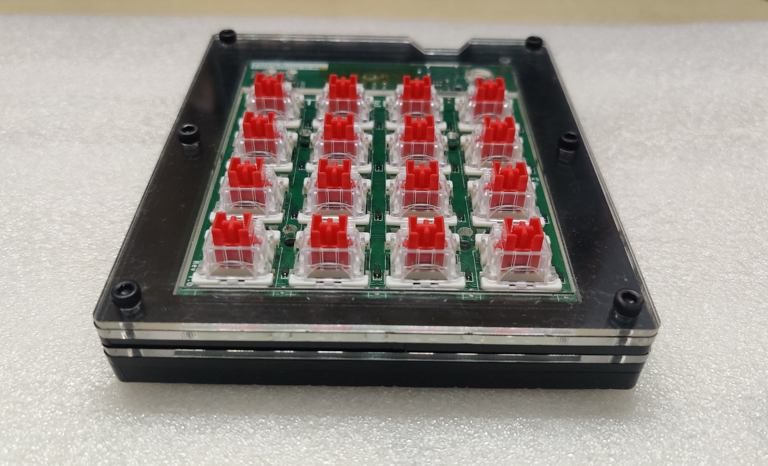
Images/Sandwich_Case/Assembly/Sandwich_Case_AS_5.jpg
