atechofficials/protokeeb/Images/Sandwich_Case/Assembly/Sandwich_Case_AS_6.jpg

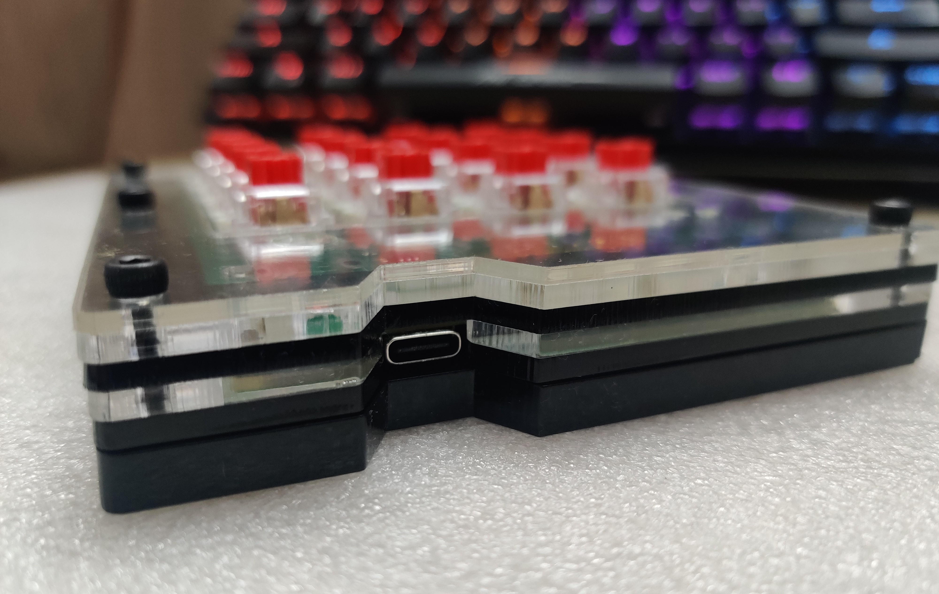
Images/Sandwich_Case/Assembly/Sandwich_Case_AS_6.jpg
